klandingham/Blinds_Control/Example_Projects/Servo_Adapter_for_Automated_Blinds/images/df64a273555f48d18f35c3c6244d9a91_preview_featured.jpg

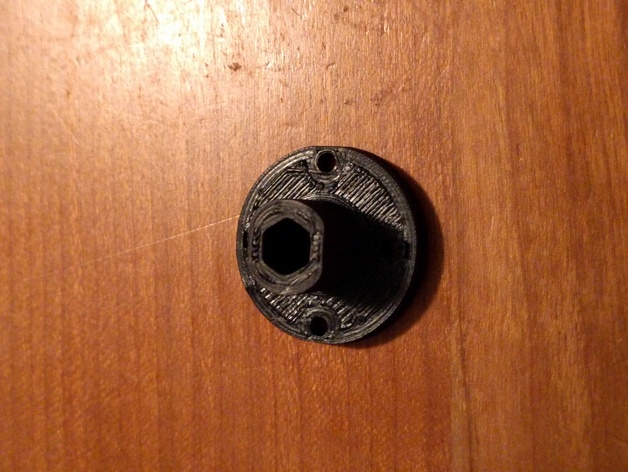
Example_Projects/Servo_Adapter_for_Automated_Blinds/images/df64a273555f48d18f35c3c6244d9a91_preview_featured.jpg
