klandingham/Blinds_Control/Example_Projects/Servo_adapter_for_blinds/images/5d1fb73a9985321ed66258ca8657291f_preview_featured.jpg

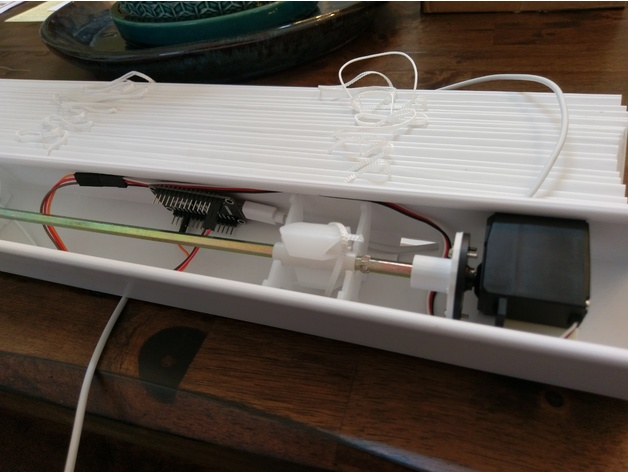
Example_Projects/Servo_adapter_for_blinds/images/5d1fb73a9985321ed66258ca8657291f_preview_featured.jpg
