klandingham/Blinds_Control/Datasheets/VS1838 datasheet_files/1_data/13673994358968836068.jpeg

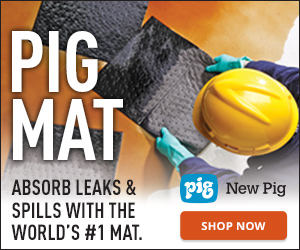
Datasheets/VS1838 datasheet_files/1_data/13673994358968836068.jpeg
