klandingham/Blinds_Control/Diagrams/74HC595_IO_expansion_sample_circuit.jpg

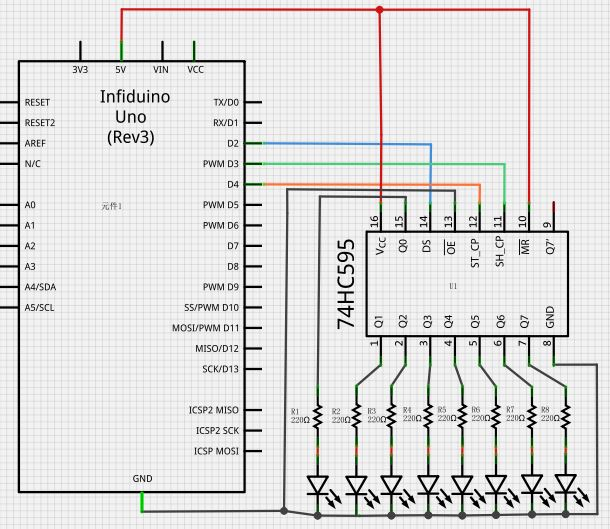
Diagrams/74HC595_IO_expansion_sample_circuit.jpg
