klandingham/Blinds_Control/Diagrams/Board Layout Labeled.jpg

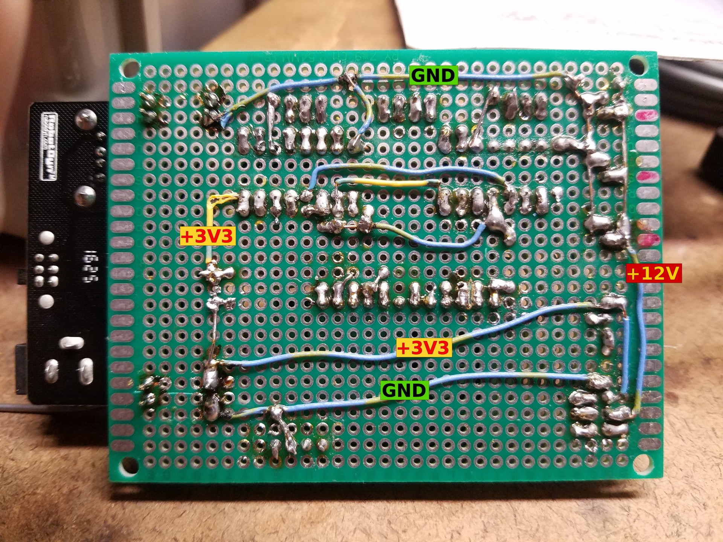
Diagrams/Board Layout Labeled.jpg
