klandingham/Blinds_Control/Diagrams/Breadboard/v2/Breadboard-2.jpg

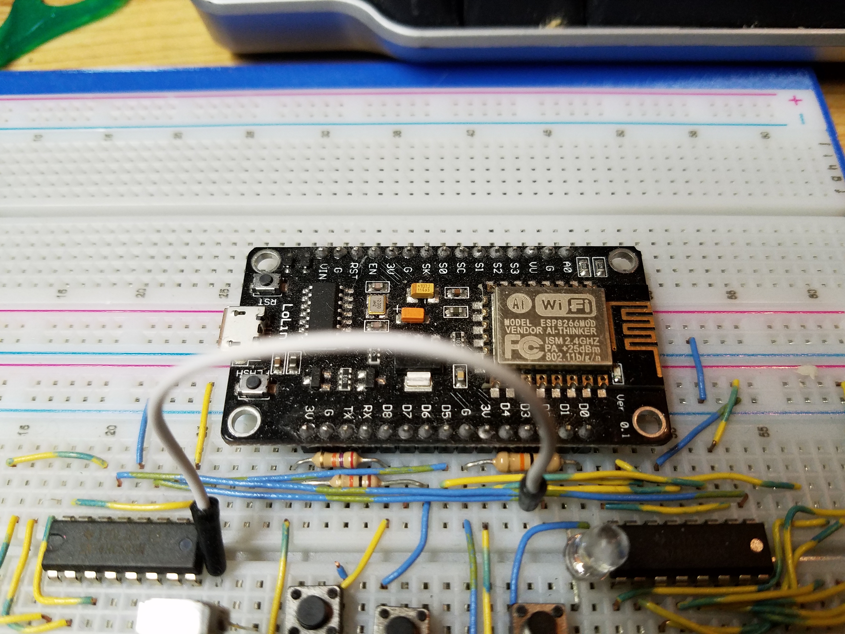
Diagrams/Breadboard/v2/Breadboard-2.jpg
