klandingham/Blinds_Control/Diagrams/Breadboard/v2/Breadboard-3.jpg

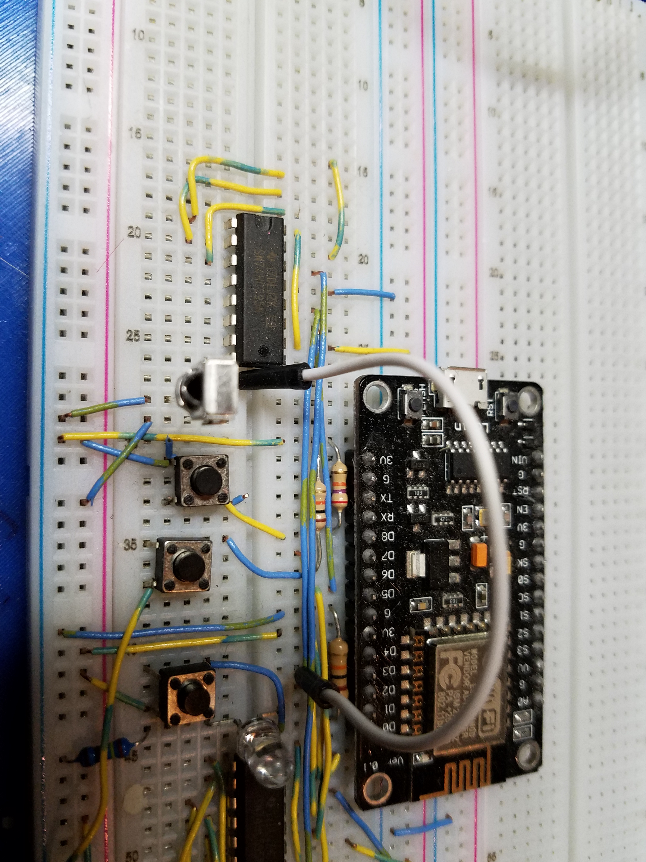
Diagrams/Breadboard/v2/Breadboard-3.jpg
