klandingham/Blinds_Control/Diagrams/J7_pins.jpg

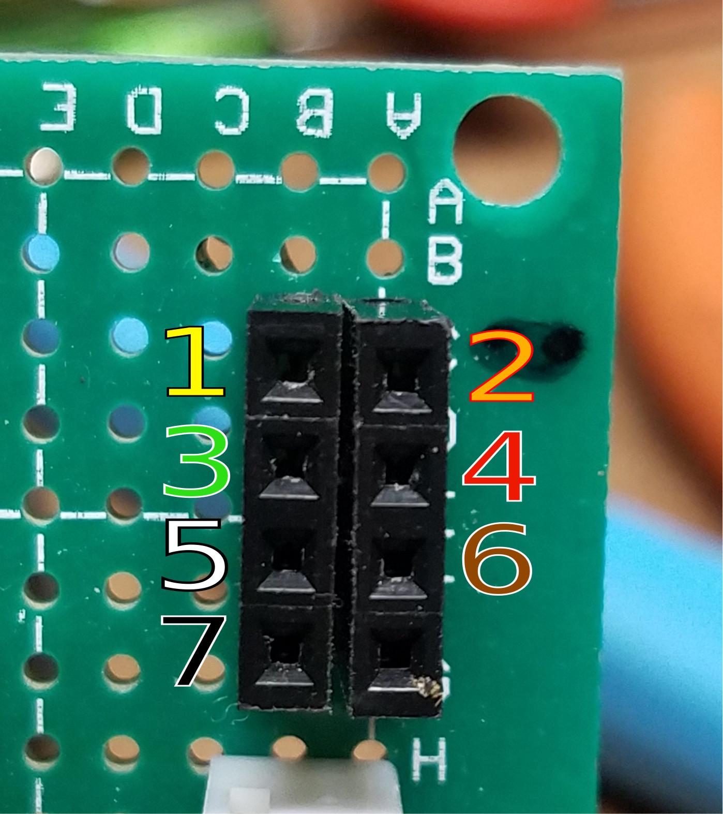
Diagrams/J7_pins.jpg
