klandingham/Blinds_Control/Diagrams/pushbutton-diagram.jpg

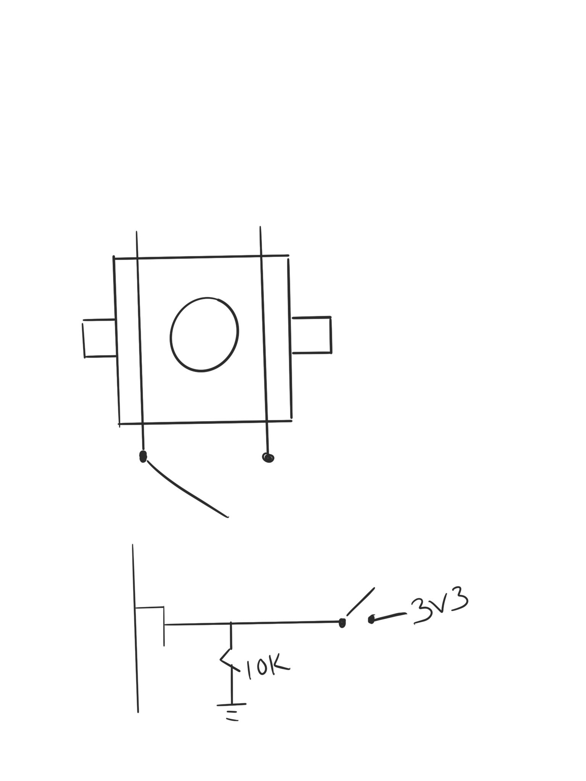
Diagrams/pushbutton-diagram.jpg
