klandingham/Blinds_Control/Example_Projects/Automated_window_blinds/images/0dbd72139b1b72931606092e1da129da_preview_featured.jpg

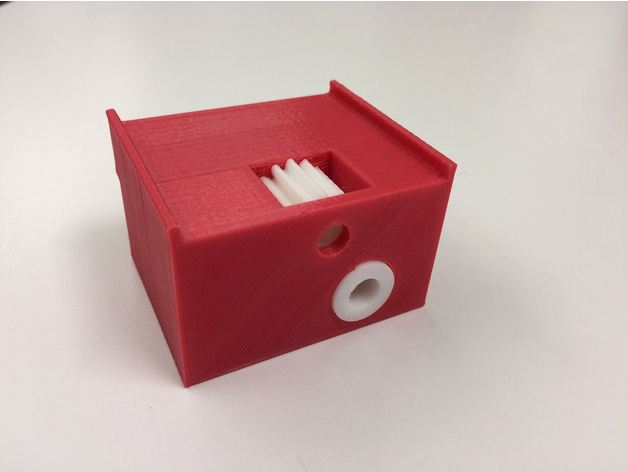
Example_Projects/Automated_window_blinds/images/0dbd72139b1b72931606092e1da129da_preview_featured.jpg
