klandingham/Blinds_Control/Example_Projects/Automated_window_blinds/images/2a1e8ae209445f8ed7df08887682355c_preview_featured.jpg

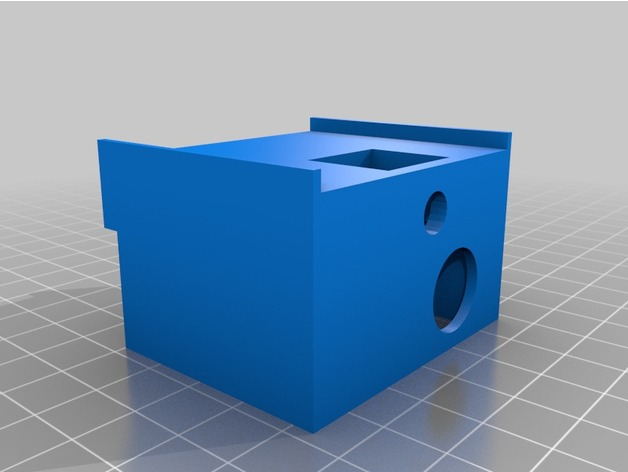
Example_Projects/Automated_window_blinds/images/2a1e8ae209445f8ed7df08887682355c_preview_featured.jpg
