klandingham/Blinds_Control/Example_Projects/Automated_window_blinds/images/3be72de2d3ea145a1b588abaab555e87_preview_featured.jpg

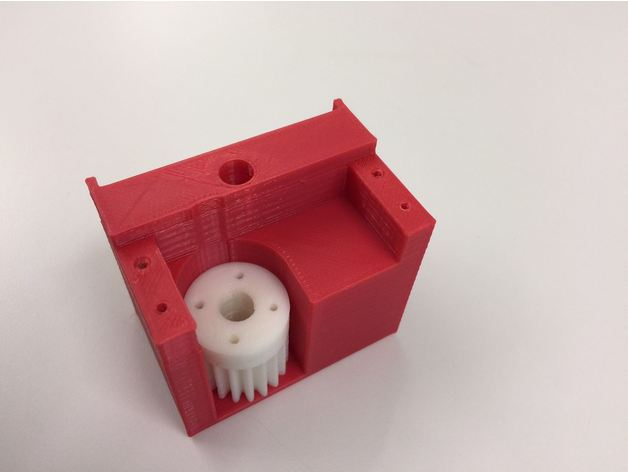
Example_Projects/Automated_window_blinds/images/3be72de2d3ea145a1b588abaab555e87_preview_featured.jpg
