klandingham/Blinds_Control/Example_Projects/Automated_window_blinds/images/7c7b84c2f0f5334c513f18091b792038_preview_featured.jpg

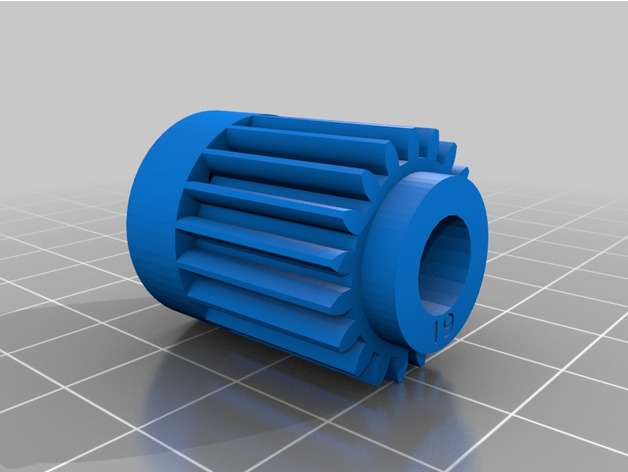
Example_Projects/Automated_window_blinds/images/7c7b84c2f0f5334c513f18091b792038_preview_featured.jpg
