klandingham/Blinds_Control/Example_Projects/Automated_window_blinds/images/51a1170ac061b8a56ec46677e9c119d1_preview_featured.jpg

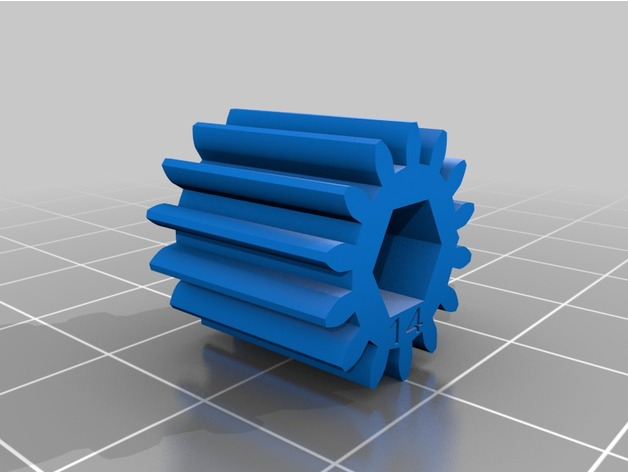
Example_Projects/Automated_window_blinds/images/51a1170ac061b8a56ec46677e9c119d1_preview_featured.jpg
