klandingham/Blinds_Control/Example_Projects/Automated_window_blinds/images/d08ca0e88c3ed342fe436adfcc059d2c_preview_featured.jpg

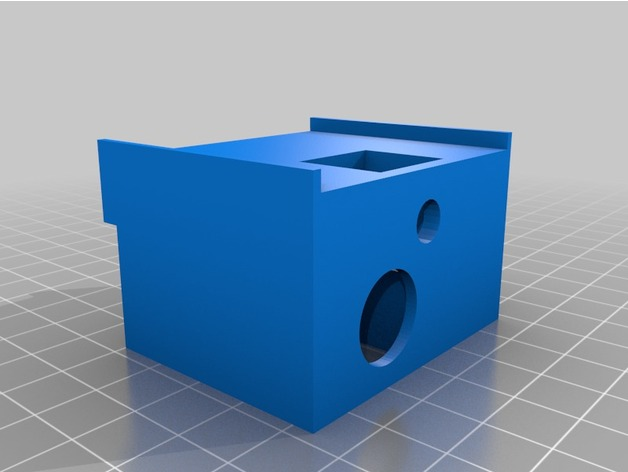
Example_Projects/Automated_window_blinds/images/d08ca0e88c3ed342fe436adfcc059d2c_preview_featured.jpg
