klandingham/Blinds_Control/Example_Projects/Blinds_Stepper_Motor_Controller/images/0ca458882b988e988b201099f90ac491_preview_featured.jpg

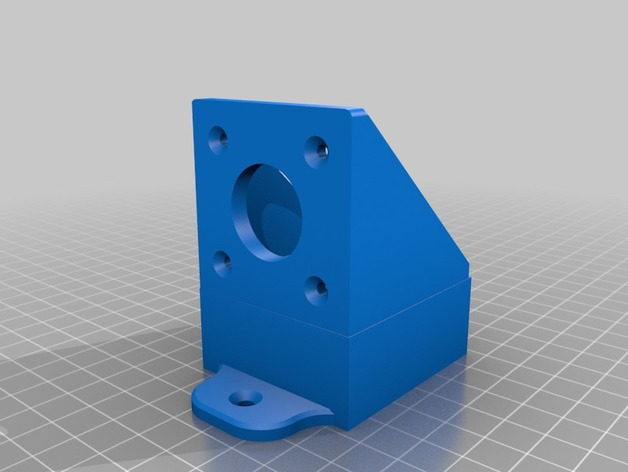
Example_Projects/Blinds_Stepper_Motor_Controller/images/0ca458882b988e988b201099f90ac491_preview_featured.jpg
