klandingham/Blinds_Control/Example_Projects/Blinds_Stepper_Motor_Controller/images/94a17963498ac2957ab965c8fd468688_preview_featured.jpg

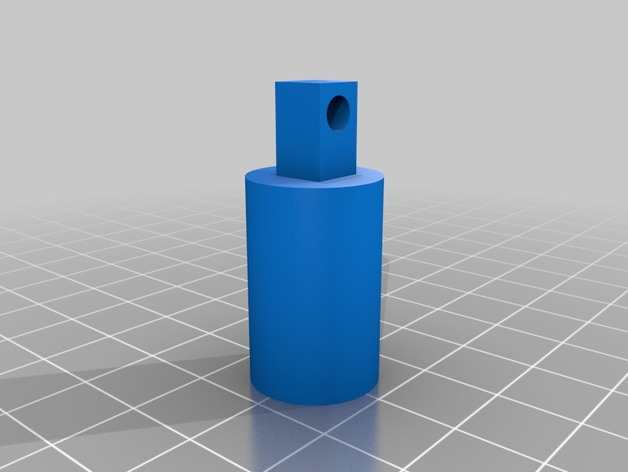
Example_Projects/Blinds_Stepper_Motor_Controller/images/94a17963498ac2957ab965c8fd468688_preview_featured.jpg
