klandingham/Blinds_Control/Example_Projects/Blinds_Stepper_Motor_Controller/images/799bad5a3b514f096e69bbc4a7896cd9_preview_featured.jpg

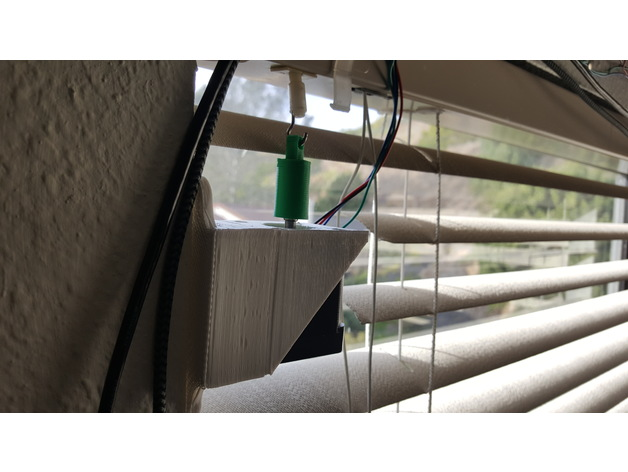
Example_Projects/Blinds_Stepper_Motor_Controller/images/799bad5a3b514f096e69bbc4a7896cd9_preview_featured.jpg
