klandingham/Blinds_Control/Example_Projects/Blinds_Stepper_Motor_Controller/images/d0096ec6c83575373e3a21d129ff8fef_preview_featured.jpg

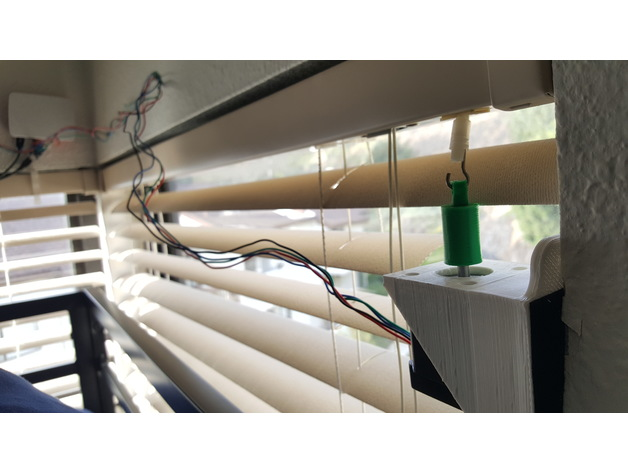
Example_Projects/Blinds_Stepper_Motor_Controller/images/d0096ec6c83575373e3a21d129ff8fef_preview_featured.jpg
