klandingham/Blinds_Control/Example_Projects/Blinds_Stepper_Motor_Controller/images/f3ccdd27d2000e3f9255a7e3e2c48800_preview_featured.jpg

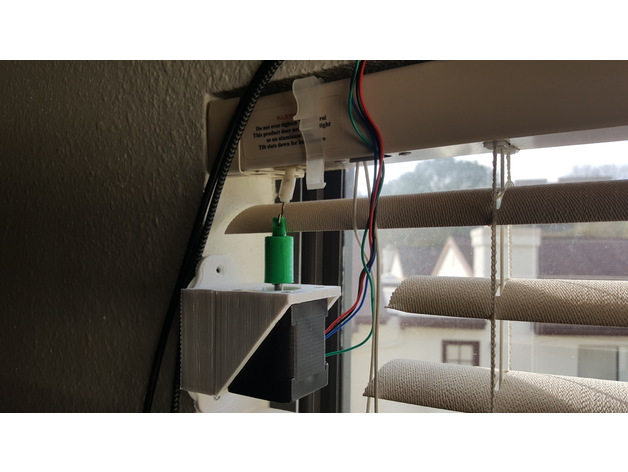
Example_Projects/Blinds_Stepper_Motor_Controller/images/f3ccdd27d2000e3f9255a7e3e2c48800_preview_featured.jpg
