klandingham/Blinds_Control/Example_Projects/Servo_Adapter_for_Automated_Blinds/images/8d56957c13c70d7b545bc574395df51b_preview_featured.jpg

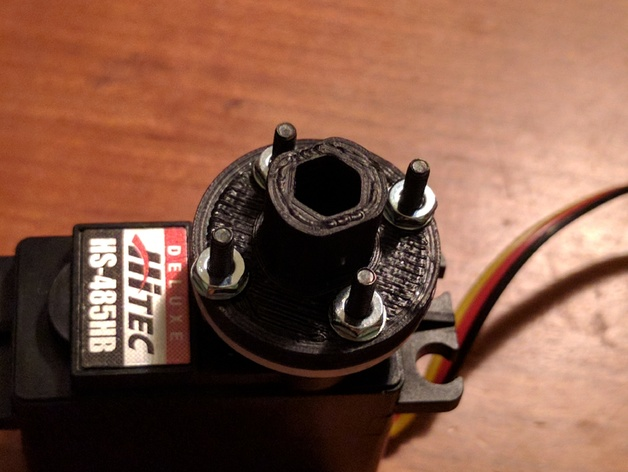
Example_Projects/Servo_Adapter_for_Automated_Blinds/images/8d56957c13c70d7b545bc574395df51b_preview_featured.jpg
