klandingham/Blinds_Control/Example_Projects/Servo_Adapter_for_Automated_Blinds/images/43b85763882b75d2b69c953d2dd04455_preview_featured.jpg

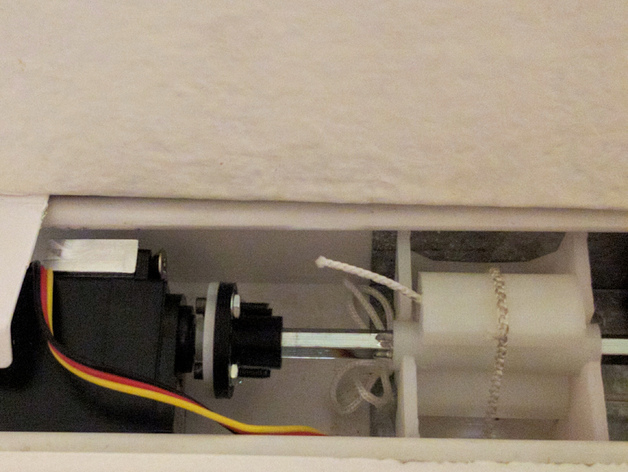
Example_Projects/Servo_Adapter_for_Automated_Blinds/images/43b85763882b75d2b69c953d2dd04455_preview_featured.jpg
