klandingham/Blinds_Control/Example_Projects/Servo_Adapter_for_Automated_Blinds/images/0583f7e29a5a532bcb58fbe3828fd911_preview_featured.jpg

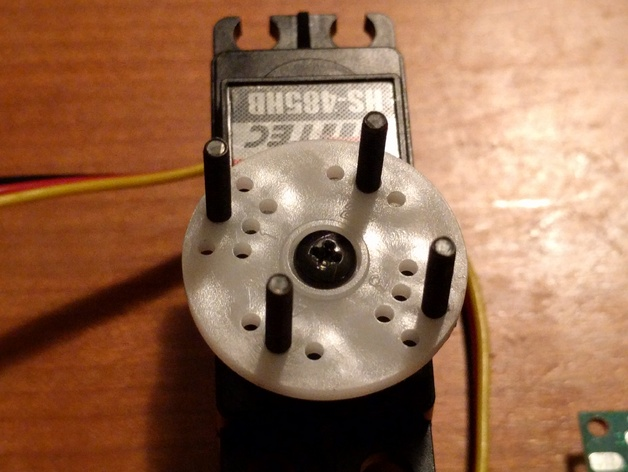
Example_Projects/Servo_Adapter_for_Automated_Blinds/images/0583f7e29a5a532bcb58fbe3828fd911_preview_featured.jpg
