klandingham/Blinds_Control/Example_Projects/Servo_Adapter_for_Automated_Blinds/images/242499b90d92d8a3c1900d62b4687f6d_preview_featured.jpg

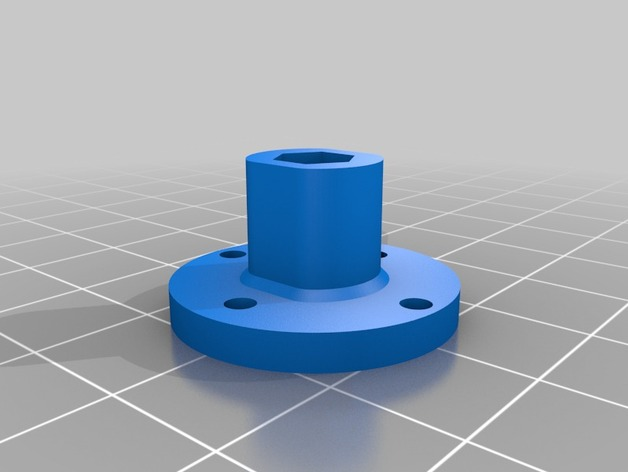
Example_Projects/Servo_Adapter_for_Automated_Blinds/images/242499b90d92d8a3c1900d62b4687f6d_preview_featured.jpg
