klandingham/Blinds_Control/Example_Projects/Servo_adapter_for_blinds/images/8e7e8af2247d28f97953c48f6f39e9a5_preview_featured.jpg

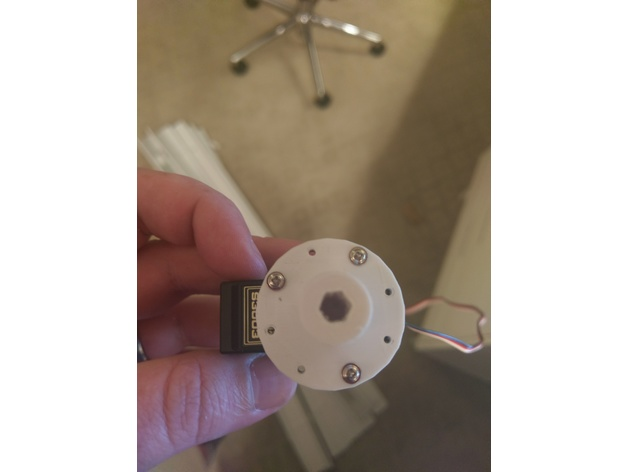
Example_Projects/Servo_adapter_for_blinds/images/8e7e8af2247d28f97953c48f6f39e9a5_preview_featured.jpg
