klandingham/Blinds_Control/Example_Projects/Servo_adapter_for_blinds/images/4008a9b219bc578ee4de48e5d4f73412_preview_featured.jpg

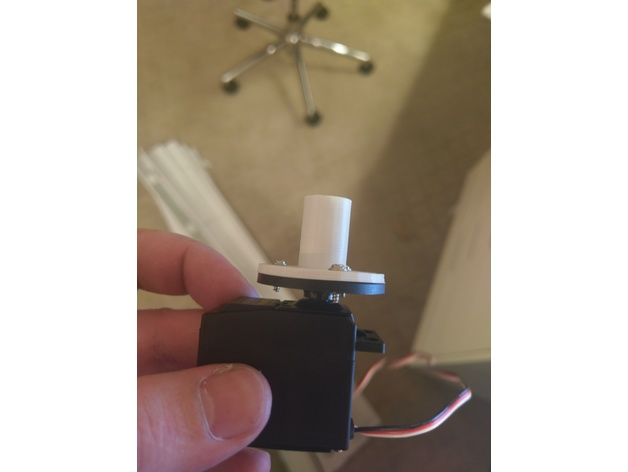
Example_Projects/Servo_adapter_for_blinds/images/4008a9b219bc578ee4de48e5d4f73412_preview_featured.jpg
