klandingham/Blinds_Control/Example_Projects/Servo_adapter_for_blinds/images/8679c8f7650d90e7cc76d3c26cc39134_preview_featured.jpg

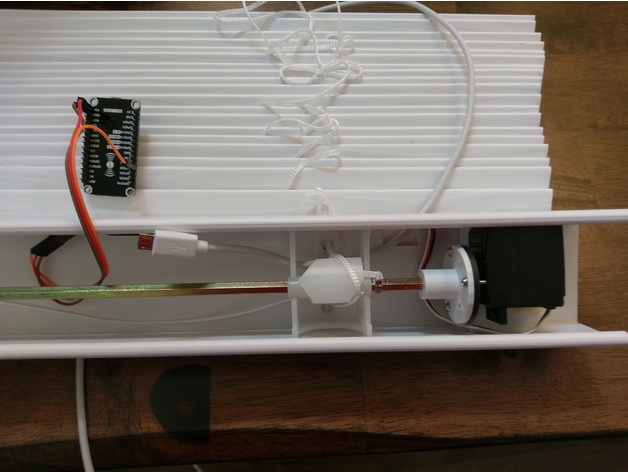
Example_Projects/Servo_adapter_for_blinds/images/8679c8f7650d90e7cc76d3c26cc39134_preview_featured.jpg
