klandingham/Blinds_Control/Example_Projects/Servo_adapter_for_blinds/images/c9348f00d997d8b843449cc2bac39666_preview_featured.jpg

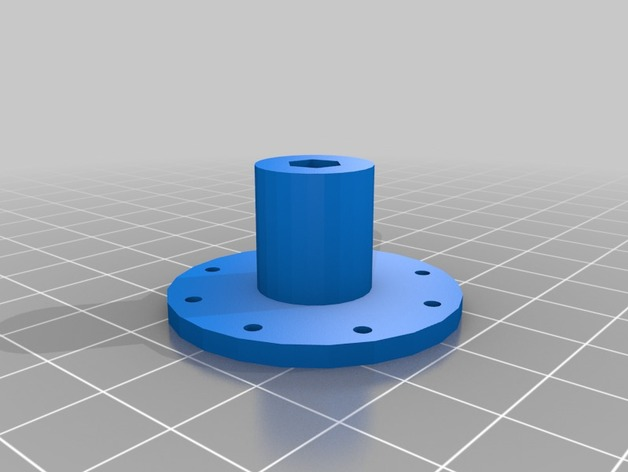
Example_Projects/Servo_adapter_for_blinds/images/c9348f00d997d8b843449cc2bac39666_preview_featured.jpg
