klandingham/Blinds_Control/Example_Projects/Servo_adapter_for_blinds/images/f5c94f27fc36e1c8725ffeb552db501e_preview_featured.jpg

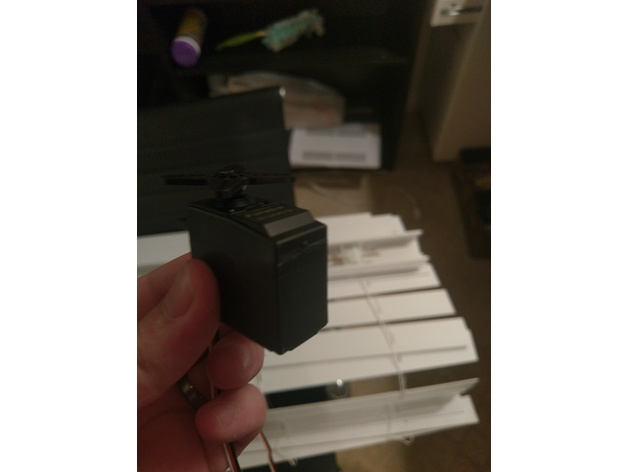
Example_Projects/Servo_adapter_for_blinds/images/f5c94f27fc36e1c8725ffeb552db501e_preview_featured.jpg
