klandingham/Blinds_Control/Example_Projects/WiFi_Window-Blinds_Roller/images/7b7e7c0269467608b5808af1a2d691ca_preview_featured.jpg

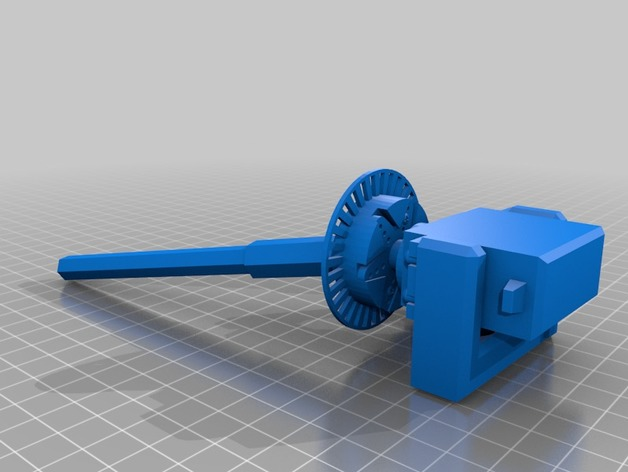
Example_Projects/WiFi_Window-Blinds_Roller/images/7b7e7c0269467608b5808af1a2d691ca_preview_featured.jpg
