klandingham/Blinds_Control/Example_Projects/WiFi_Window-Blinds_Roller/images/9c8a4cd324916dcc4e85334bb4fedf4f_preview_featured.JPG

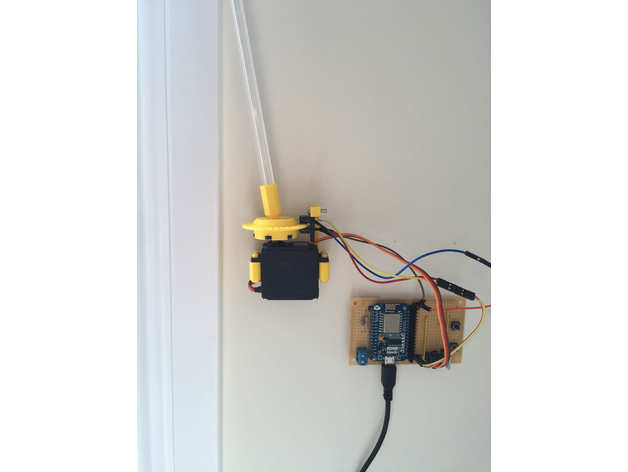
Example_Projects/WiFi_Window-Blinds_Roller/images/9c8a4cd324916dcc4e85334bb4fedf4f_preview_featured.JPG
