klandingham/Blinds_Control/Example_Projects/WiFi_Window-Blinds_Roller/images/47e4459eb694de2b554587ecafb3ef61_preview_featured.jpg

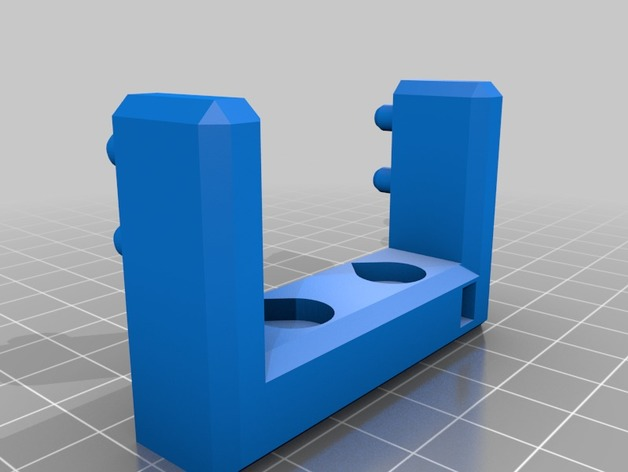
Example_Projects/WiFi_Window-Blinds_Roller/images/47e4459eb694de2b554587ecafb3ef61_preview_featured.jpg
