klandingham/Blinds_Control/Example_Projects/WiFi_Window-Blinds_Roller/images/64f70ef4e7e904f5829ffbd56e4282fa_preview_featured.jpg

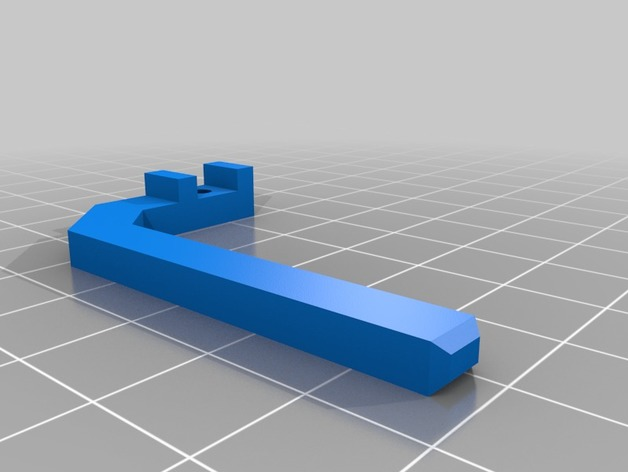
Example_Projects/WiFi_Window-Blinds_Roller/images/64f70ef4e7e904f5829ffbd56e4282fa_preview_featured.jpg
