klandingham/Blinds_Control/Example_Projects/WiFi_Window-Blinds_Roller/images/93ce8574e1e4e3efcc80637c74880ca0_preview_featured.jpg

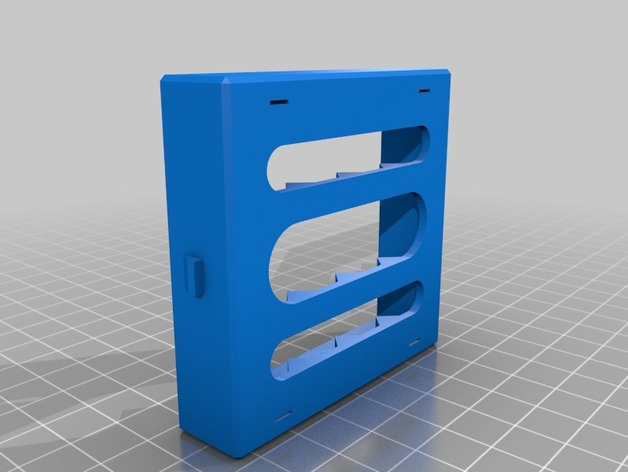
Example_Projects/WiFi_Window-Blinds_Roller/images/93ce8574e1e4e3efcc80637c74880ca0_preview_featured.jpg
