klandingham/Blinds_Control/Example_Projects/WiFi_Window-Blinds_Roller/images/aa77651dd114ddc3b98a7daae5970775_preview_featured.jpg

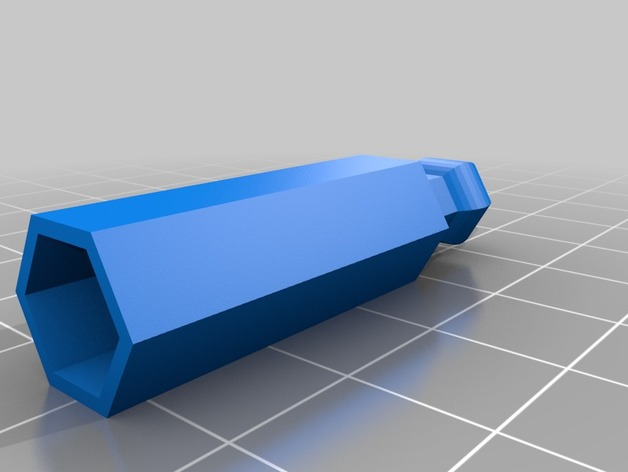
Example_Projects/WiFi_Window-Blinds_Roller/images/aa77651dd114ddc3b98a7daae5970775_preview_featured.jpg
