klandingham/Blinds_Control/Example_Projects/Blinds_Stepper_Motor_Controller/files/motor-container.stl

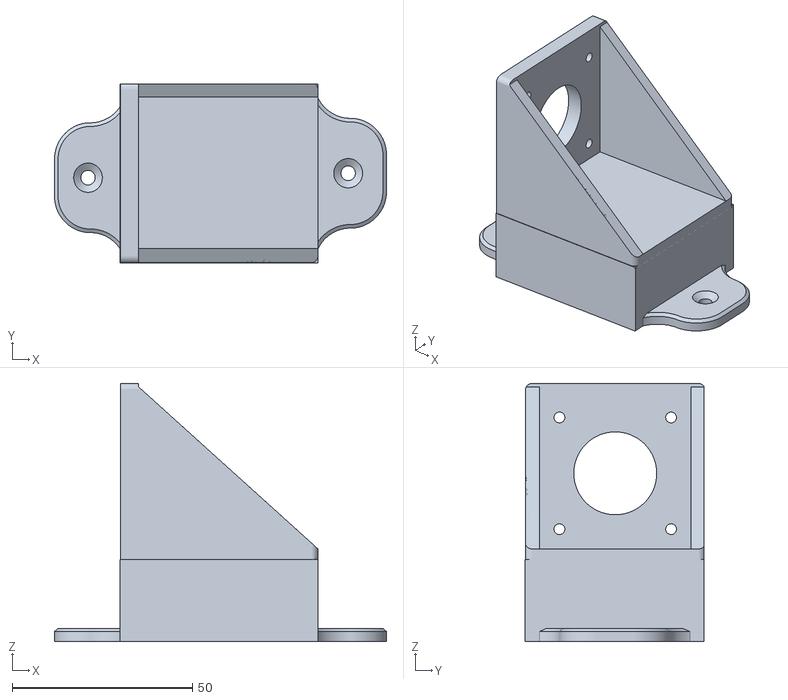
[picture p52: CAD file, 2019-06-21]
Example_Projects/Blinds_Stepper_Motor_Controller/files/motor-container.stl
92.2 x 49.8 x 71.8
