klandingham/Blinds_Control/Example_Projects/BlindsRodAdapter.STL

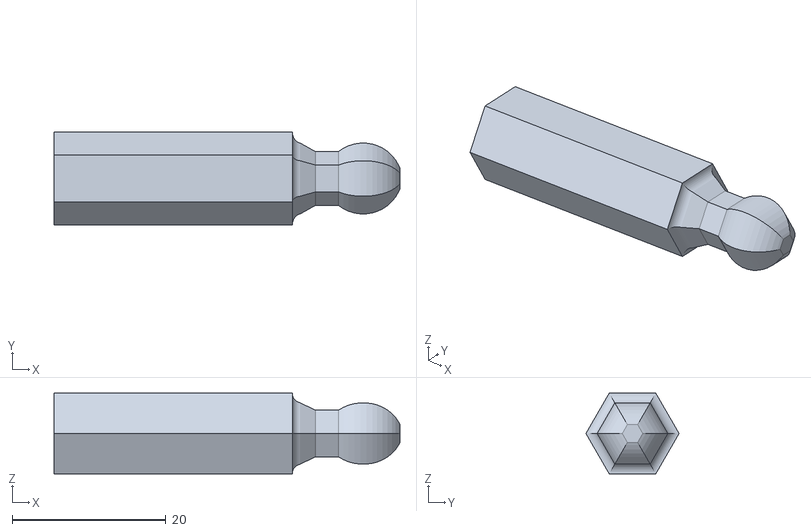
[picture p53: CAD file, 2019-06-21]
Example_Projects/BlindsRodAdapter.STL
45.0 x 12.1 x 10.5
