klandingham/Blinds_Control/stl/Original Design/slip-clutch-plate-v1.stl

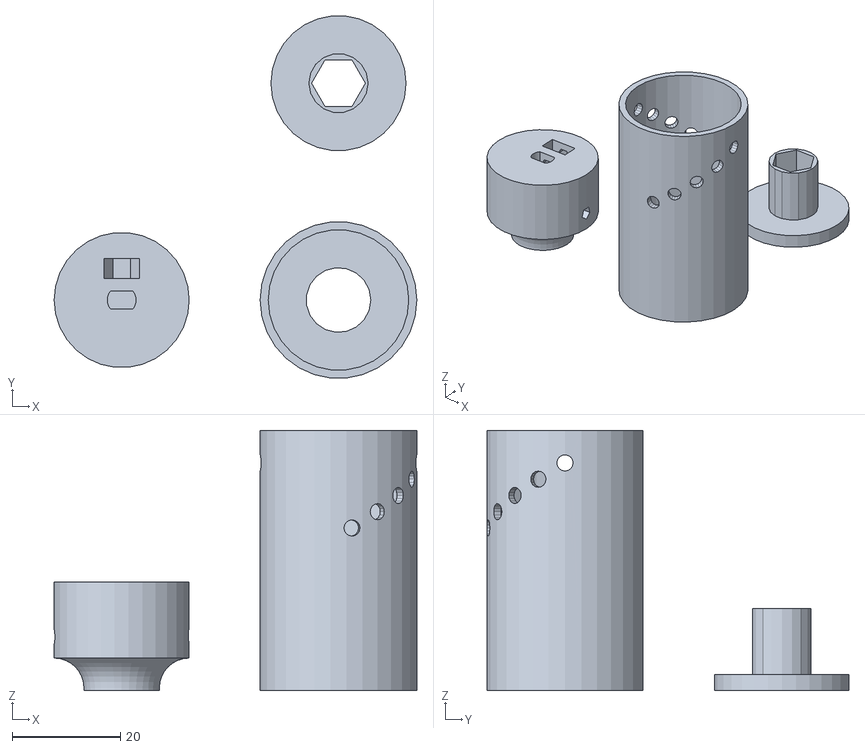
[picture p54: CAD file, 2019-06-21]
stl/Original Design/slip-clutch-plate-v1.stl
66.9 x 66.8 x 48.0
