klandingham/Blinds_Control/stl/Rod Sleeve Mod - 7.9.stl

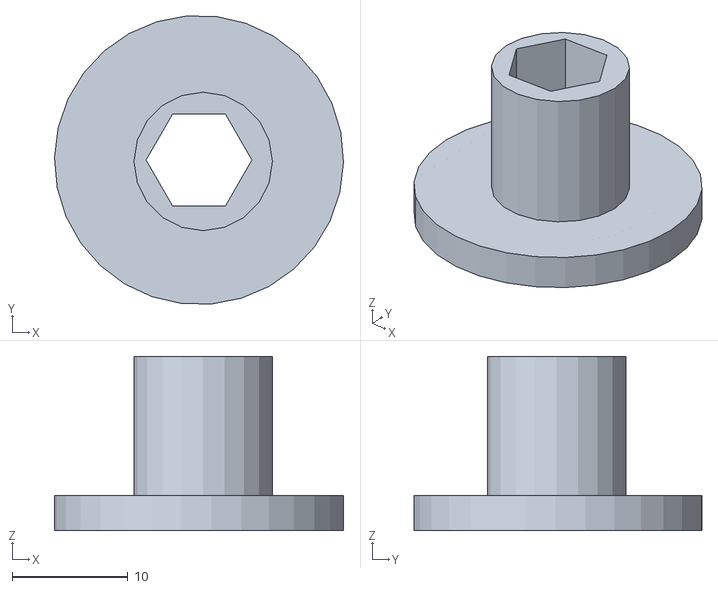
[picture p55: CAD file, 2019-06-21]
stl/Rod Sleeve Mod - 7.9.stl
24.9 x 24.8 x 15.0
