klandingham/Blinds_Control/Example_Projects/Automated_window_blinds/files/Offset_Geared_Servo_Blinds.stl.stl

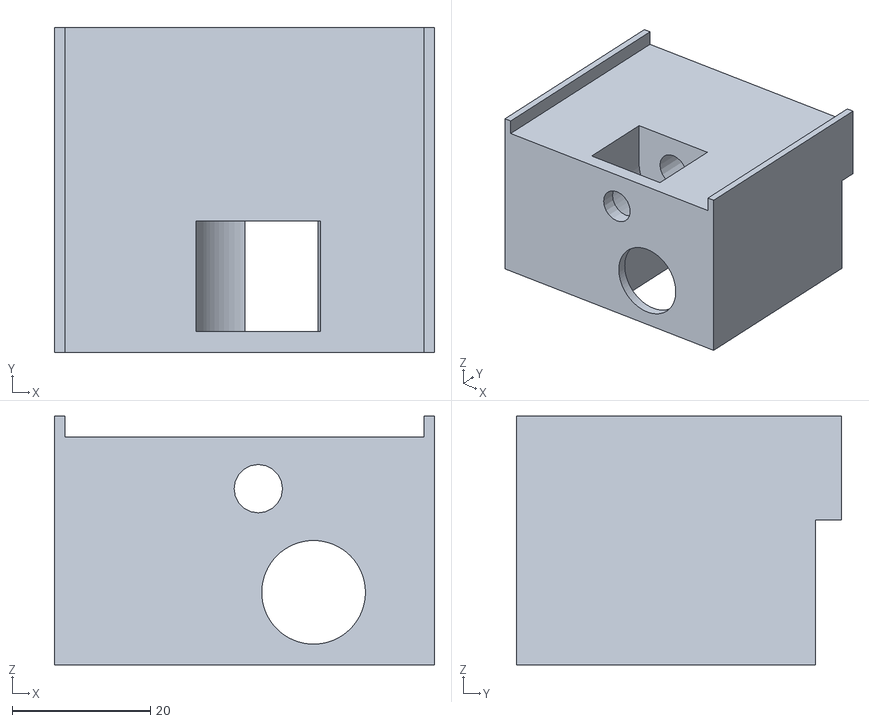
[picture p56: CAD file, 2019-06-21]
Example_Projects/Automated_window_blinds/files/Offset_Geared_Servo_Blinds.stl.stl
55.0 x 47.0 x 36.0
