klandingham/Blinds_Control/Example_Projects/WiFi_Window-Blinds_Roller/files/ServoMount.STL

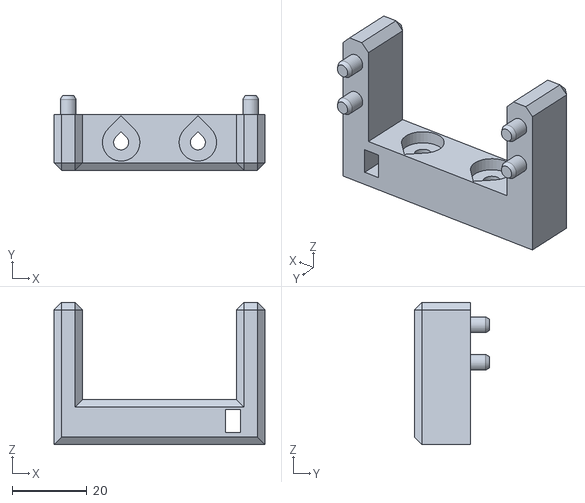
[picture p57: CAD file, 2019-06-21]
Example_Projects/WiFi_Window-Blinds_Roller/files/ServoMount.STL
56.3 x 20.0 x 38.0
