klandingham/Blinds_Control/stl/box_cover/button_board_size_test_1.stl

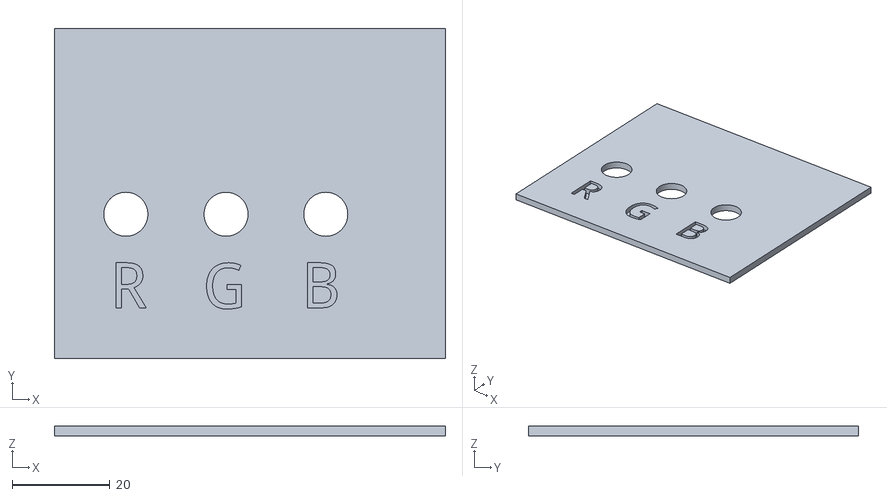
[picture p58: CAD file, 2019-07-14]
stl/box_cover/button_board_size_test_1.stl
80.0 x 67.5 x 2.00
