klandingham/Blinds_Control/stl/Rod Sleeve Mod.stl

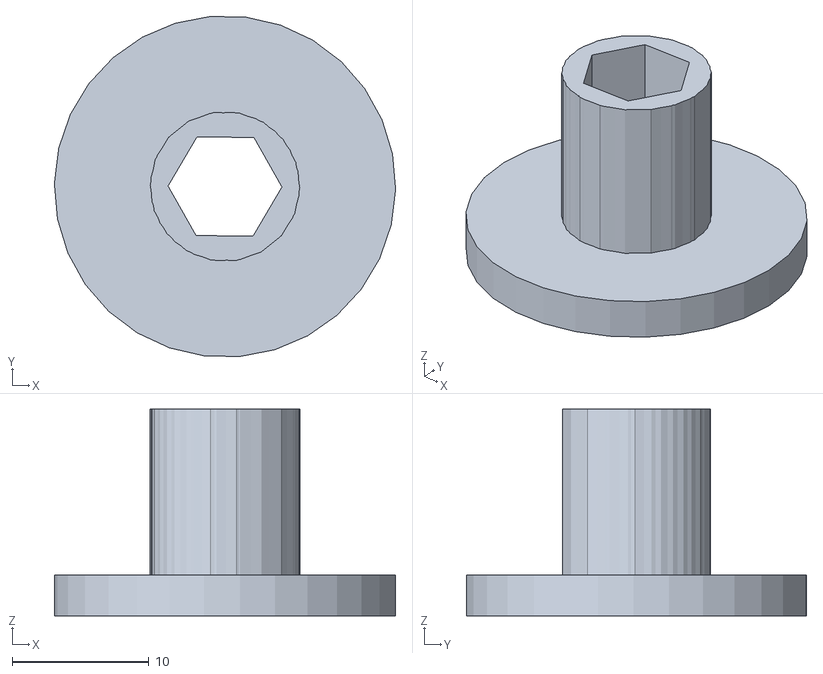
[picture p59: CAD file, 2019-06-21]
stl/Rod Sleeve Mod.stl
24.9 x 24.8 x 15.1
