klandingham/Blinds_Control/Example_Projects/Blinds_Automation_-_using_LinkIt_ONE/servo_horn_v2.stl

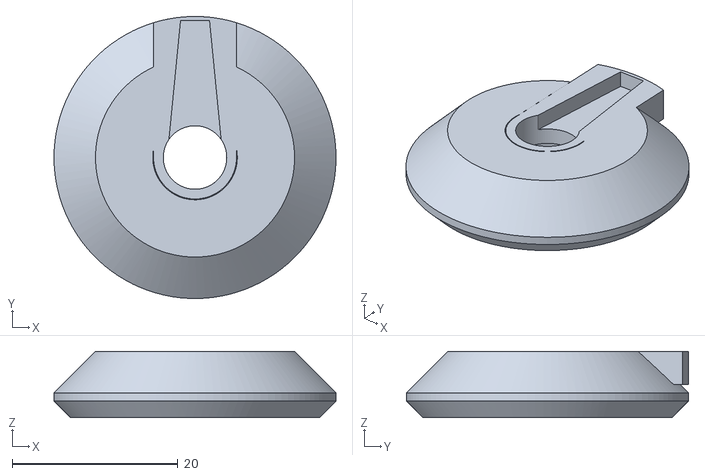
[picture p60: CAD file, 2019-06-21]
Example_Projects/Blinds_Automation_-_using_LinkIt_ONE/servo_horn_v2.stl
34.0 x 34.0 x 8.00
