klandingham/Blinds_Control/Example_Projects/WiFi_Window-Blinds_Roller/files/BatteryBox-4.STL

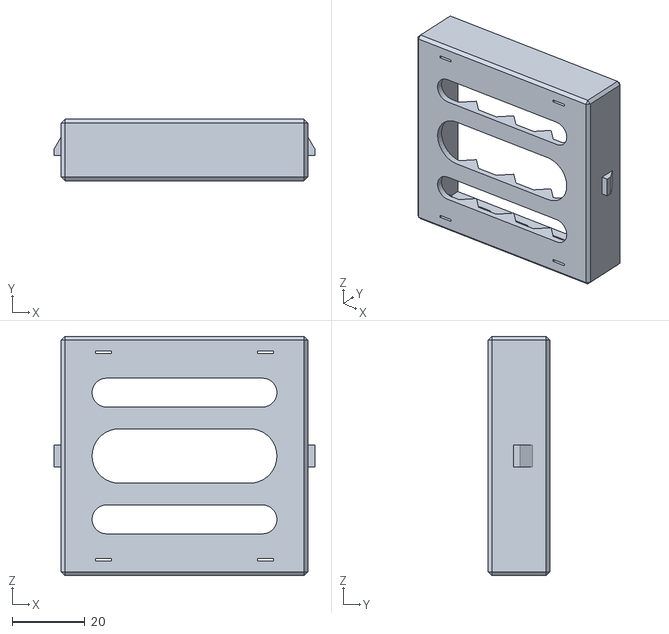
[picture p61: CAD file, 2019-06-21]
Example_Projects/WiFi_Window-Blinds_Roller/files/BatteryBox-4.STL
72.0 x 17.0 x 66.0
