klandingham/Blinds_Control/stl/box_cover/button_spacing_test.stl

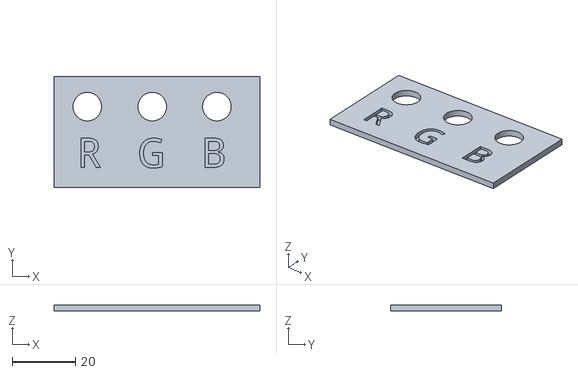
[picture p62: CAD file, 2019-07-09]
stl/box_cover/button_spacing_test.stl
65.0 x 35.0 x 2.00
