klandingham/Blinds_Control/stl/Rod Sleeve Size Test - 7.9.stl

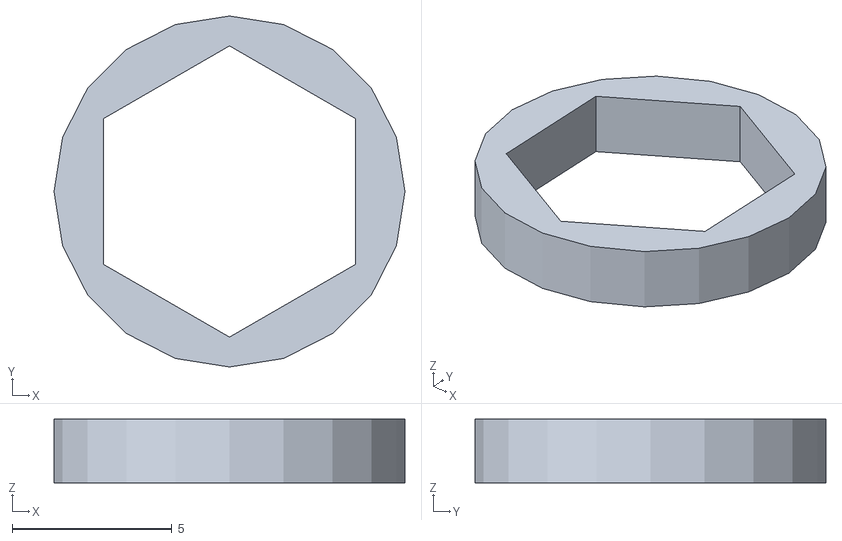
[picture p63: CAD file, 2019-06-21]
stl/Rod Sleeve Size Test - 7.9.stl
11.0 x 11.0 x 2.00
