klandingham/Blinds_Control/Example_Projects/BlindZer-master/3D STL Files/Assemly_PREVIEW.STL

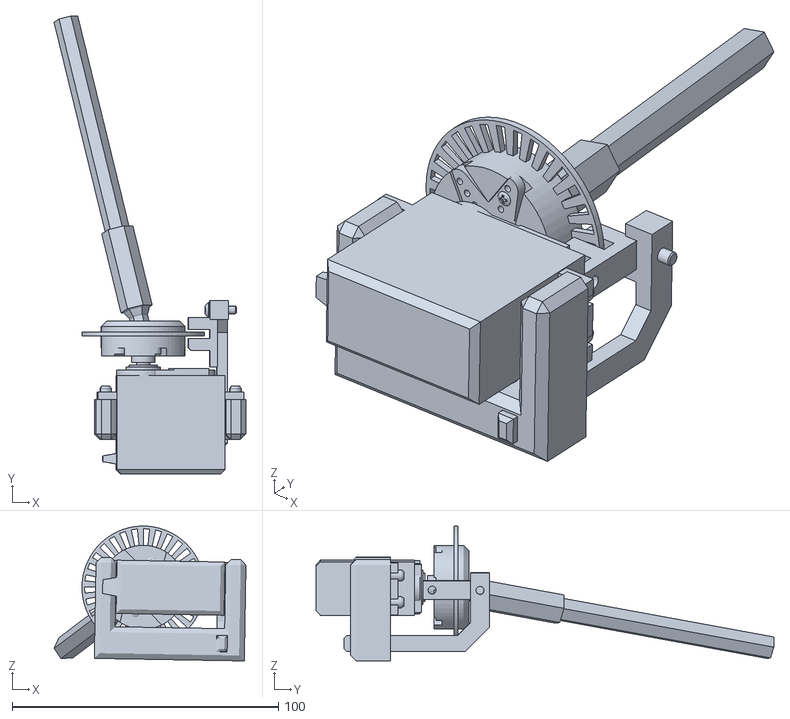
[picture p64: CAD file, 2019-06-21]
Example_Projects/BlindZer-master/3D STL Files/Assemly_PREVIEW.STL
72.1 x 171.9 x 50.6
