klandingham/Blinds_Control/stl/box_cover/button_hole_diam_test.stl

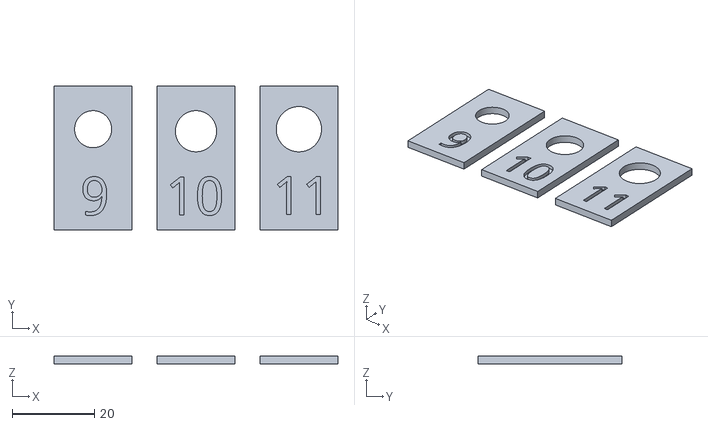
[picture p65: CAD file, 2019-07-07]
stl/box_cover/button_hole_diam_test.stl
69.0 x 35.0 x 2.00
