klandingham/Blinds_Control/stl/box_cover/box.stl

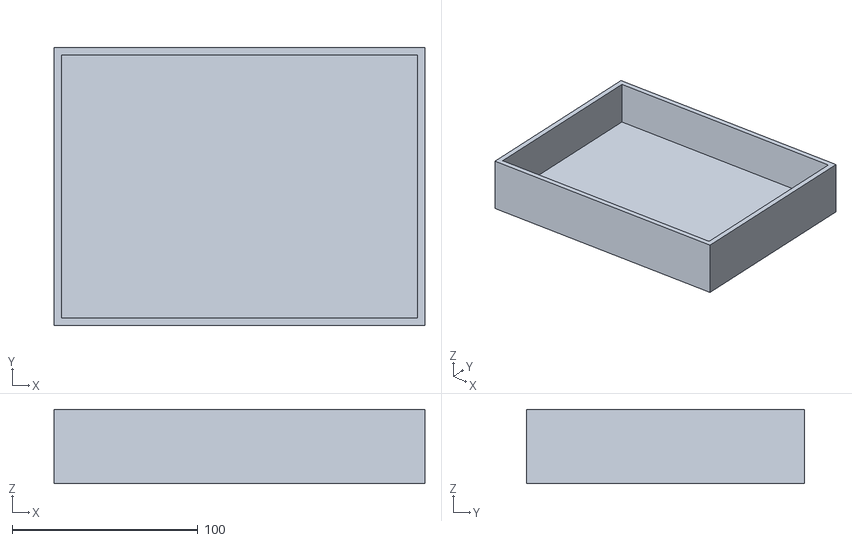
[picture p66: CAD file, 2019-07-07]
stl/box_cover/box.stl
200.0 x 150.0 x 40.0
