klandingham/Blinds_Control/stl/L Strut (thick).stl

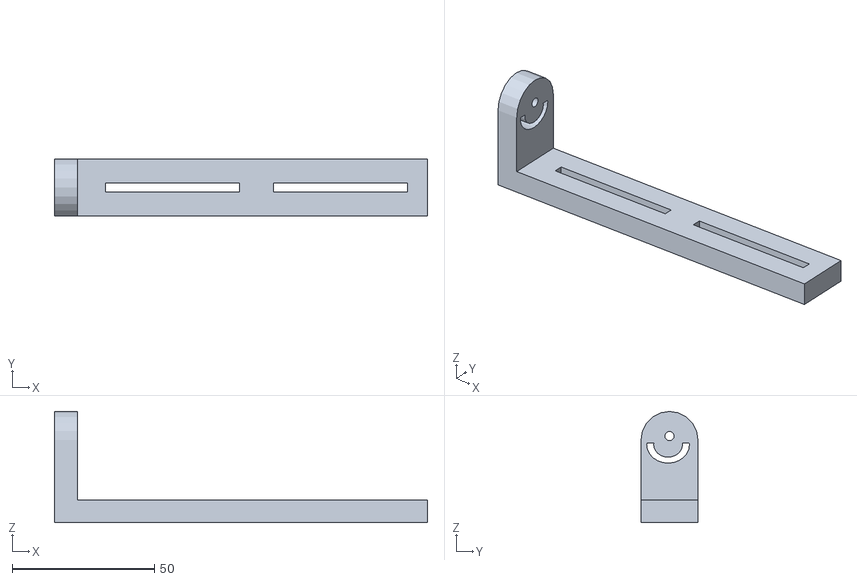
[picture p67: CAD file, 2019-06-21]
stl/L Strut (thick).stl
130.9 x 20.0 x 39.0
