klandingham/Blinds_Control/stl/Window Trim Mount (contour test smoothed).stl

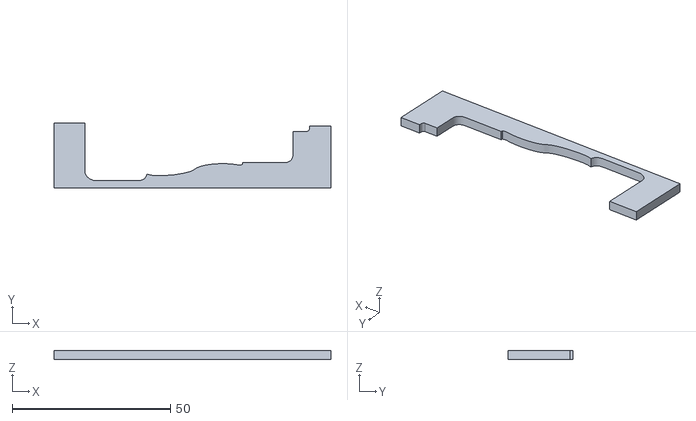
[picture p68: CAD file, 2019-06-21]
stl/Window Trim Mount (contour test smoothed).stl
87.5 x 20.6 x 2.80
