klandingham/Blinds_Control/stl/L Strut.stl

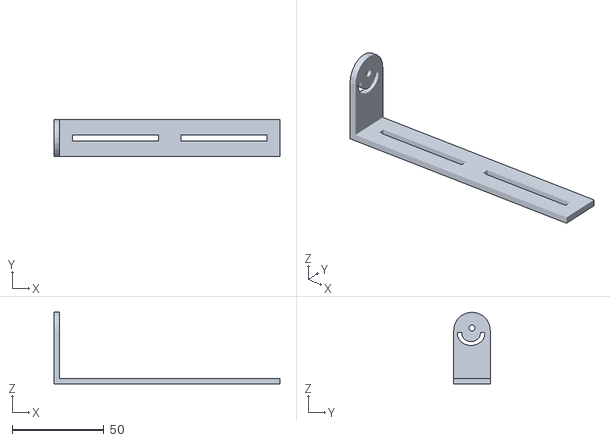
[picture p69: CAD file, 2019-06-21]
stl/L Strut.stl
123.0 x 20.0 x 39.0
