klandingham/Blinds_Control/stl/Window Trim Mount (contour test).stl

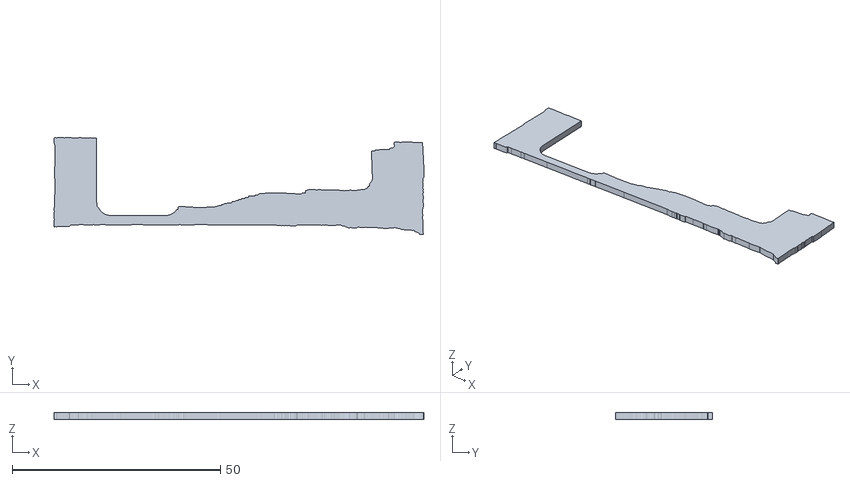
[picture p70: CAD file, 2019-06-21]
stl/Window Trim Mount (contour test).stl
88.9 x 23.4 x 1.57
