klandingham/Blinds_Control/stl/Window Trim Mount Base v3.stl

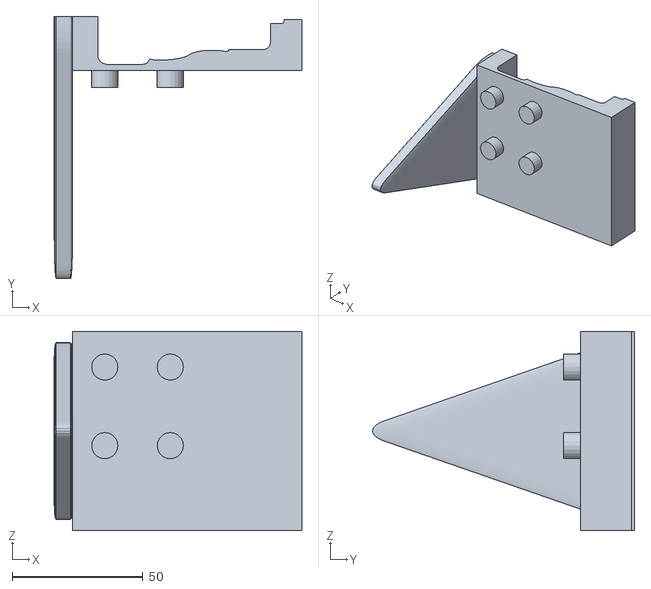
[picture p71: CAD file, 2019-06-21]
stl/Window Trim Mount Base v3.stl
94.5 x 100.0 x 76.0
