klandingham/Blinds_Control/stl/Blind Clutch Motor Hub Mod 1.stl

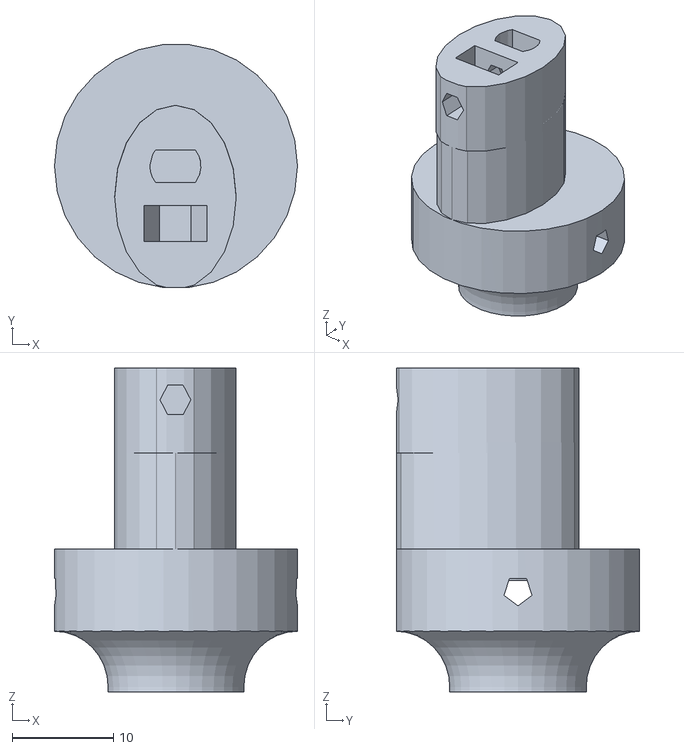
[picture p72: CAD file, 2019-06-21]
stl/Blind Clutch Motor Hub Mod 1.stl
24.0 x 24.0 x 32.0
