klandingham/Blinds_Control/stl/Blinds Clutch Spring Cup (enlarged hole).stl

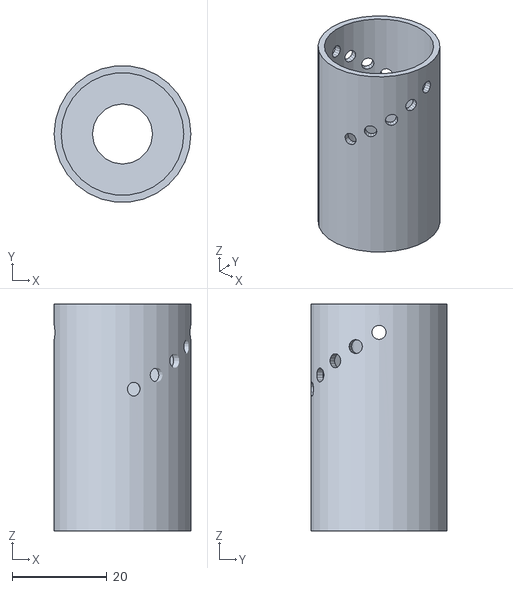
[picture p73: CAD file, 2019-06-21]
stl/Blinds Clutch Spring Cup (enlarged hole).stl
28.9 x 28.8 x 48.0
