klandingham/Blinds_Control/stl/Window Trim Mount Side Plate.stl

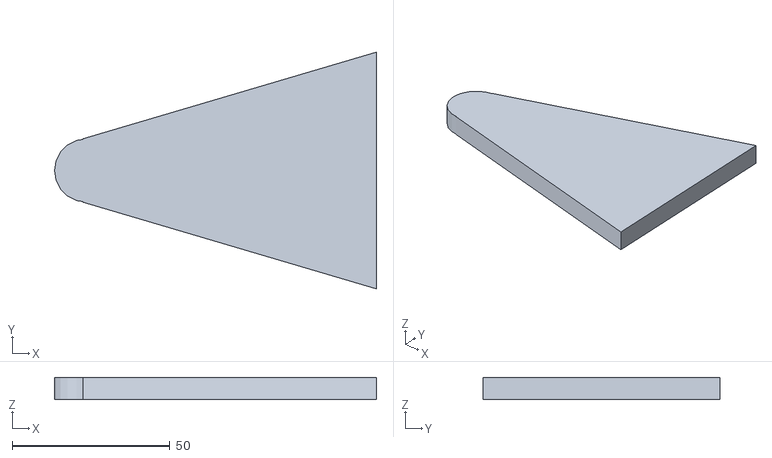
[picture p74: CAD file, 2019-06-21]
stl/Window Trim Mount Side Plate.stl
102.0 x 75.0 x 7.00
