klandingham/Blinds_Control/Diagrams/KiCAD/V3-working/V3.kicad_pcb

## KiCad design kicad/Eprommer.sch

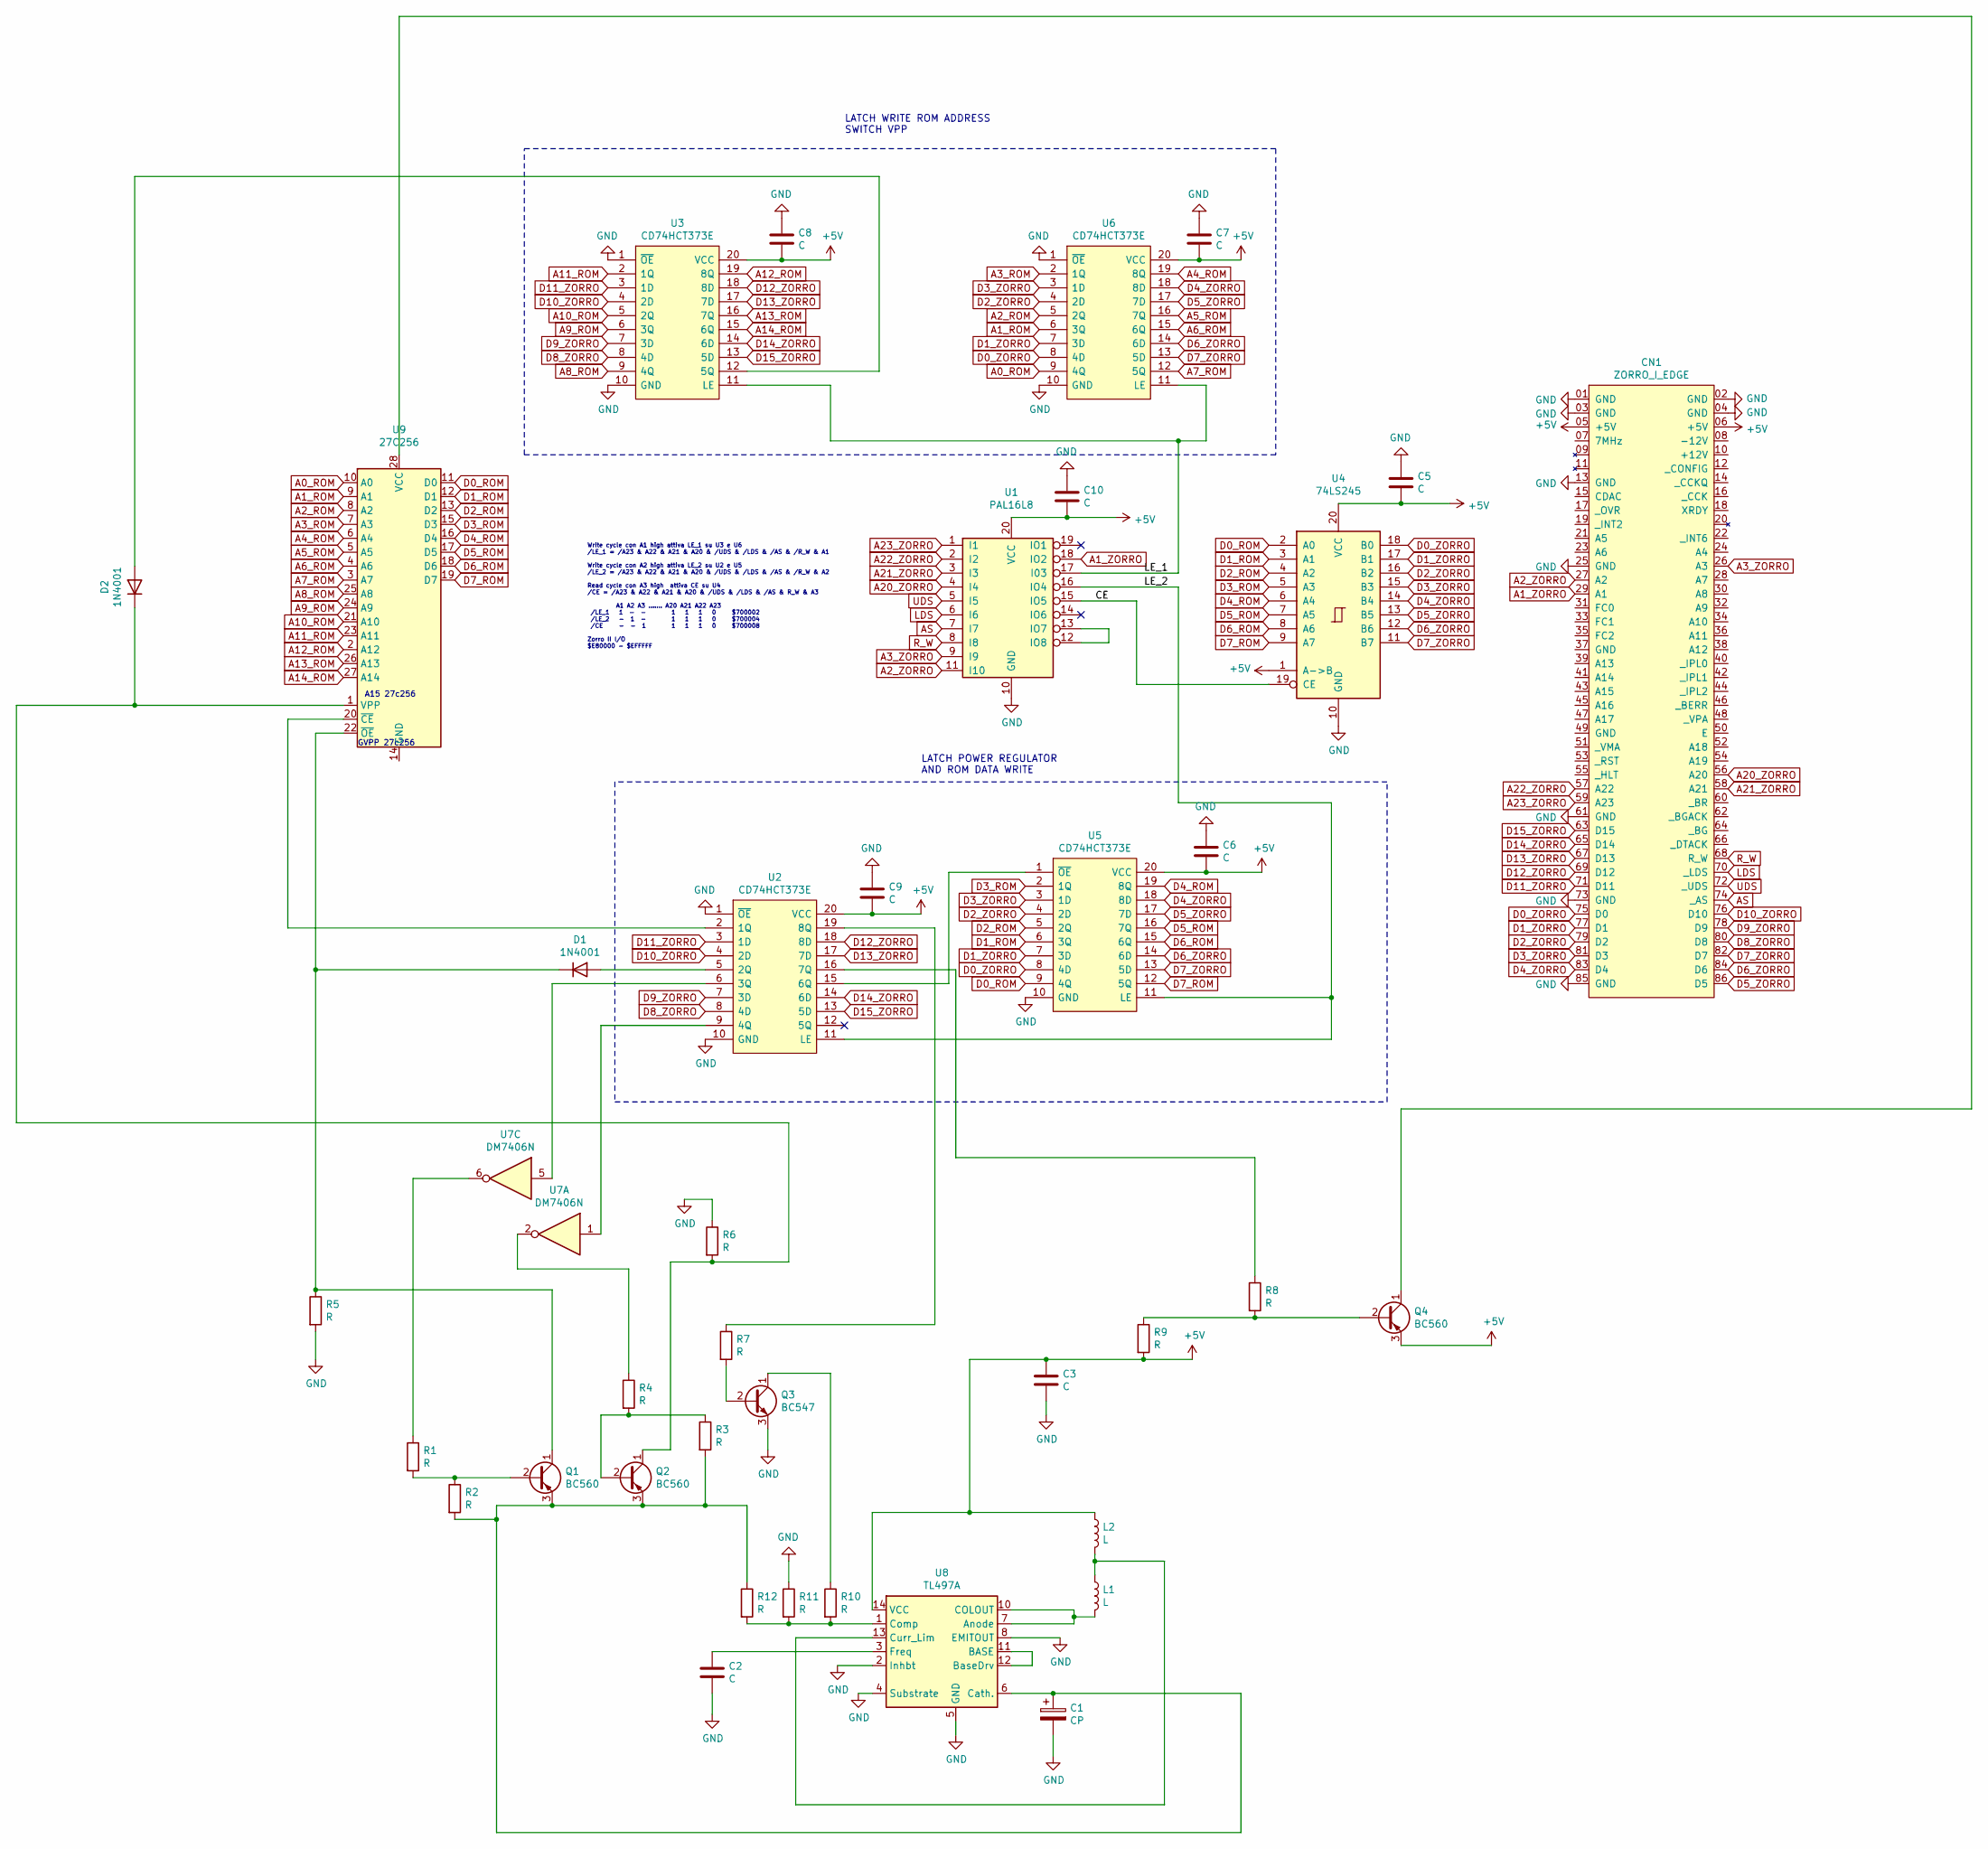
[picture p75: schematic Eprommer.sch]

Parts:
C1: CP
C2, C3, C5, C6, C7, C8, C9, C10: C
CN1: ZORRO_I_EDGE
D1, D2: 1N4001; D_DO-41_SOD81_P10.16mm_Horizontal
L1, L2: L
Q1, Q2, Q4: BC560; TO-92_Inline
Q3: BC547; TO-92_Inline
R1, R2, R3, R4, R5, R6, R7, R8, R9, R10, R11, R12: R
U1: PAL16L8
U2, U3, U5, U6: CD74HCT373E; DIP794W53P254L2540H508Q20N; Mouser Part Number 595-CD74HCT373E
U4: 74LS245
U7: DM7406N
U8: TL497A
U9: 27C256; DIP-28_W15.24mm

Connections:
+5V: C3.1, C5.2, C6.2, C7.2, C8.2, C9.2, C10.2, CN1.05 (+5V), CN1.06 (+5V), L2.1, Q4.3 (E), R9.2, U1.20 (VCC), U2.20 (VCC), U3.20 (VCC), U4.1 (A->B), U4.20 (VCC), U5.20 (VCC), U6.20 (VCC), U8.14 (VCC)
A0_ROM: U6.9 (4Q), U9.10 (A0)
A1_ROM: U6.6 (3Q), U9.9 (A1)
A1_ZORRO: CN1.29 (A1), U1.18 (IO2)
A2_ROM: U6.5 (2Q), U9.8 (A2)
A2_ZORRO: CN1.27 (A2), U1.11 (I10)
A3_ROM: U6.2 (1Q), U9.7 (A3)
A3_ZORRO: CN1.26 (A3), U1.9 (I9)
A4_ROM: U6.19 (8Q), U9.6 (A4)
A5_ROM: U6.16 (7Q), U9.5 (A5)
A6_ROM: U6.15 (6Q), U9.4 (A6)
A7_ROM: U6.12 (5Q), U9.3 (A7)
A8_ROM: U3.9 (4Q), U9.25 (A8)
A9_ROM: U3.6 (3Q), U9.24 (A9)
A10_ROM: U3.5 (2Q), U9.21 (A10)
A11_ROM: U3.2 (1Q), U9.23 (A11)
A12_ROM: U3.19 (8Q), U9.2 (A12)
A13_ROM: U3.16 (7Q), U9.26 (A13)
A14_ROM: U3.15 (6Q), U9.27 (A14)
A20_ZORRO: CN1.56 (A20), U1.4 (I4)
A21_ZORRO: CN1.58 (A21), U1.3 (I3)
A22_ZORRO: CN1.57 (A22), U1.2 (I2)
A23_ZORRO: CN1.59 (A23), U1.1 (I1)
AS: CN1.74 (_AS), U1.7 (I7)
CE: U1.15 (IO5), U4.19 (CE)
D0_ROM: U4.2 (A0), U5.9 (4Q), U9.11 (D0)
D0_ZORRO: CN1.75 (D0), U4.18 (B0), U5.8 (4D), U6.8 (4D)
D1_ROM: U4.3 (A1), U5.6 (3Q), U9.12 (D1)
D1_ZORRO: CN1.77 (D1), U4.17 (B1), U5.7 (3D), U6.7 (3D)
D2_ROM: U4.4 (A2), U5.5 (2Q), U9.13 (D2)
D2_ZORRO: CN1.79 (D2), U4.16 (B2), U5.4 (2D), U6.4 (2D)
D3_ROM: U4.5 (A3), U5.2 (1Q), U9.15 (D3)
D3_ZORRO: CN1.81 (D3), U4.15 (B3), U5.3 (1D), U6.3 (1D)
D4_ROM: U4.6 (A4), U5.19 (8Q), U9.16 (D4)
D4_ZORRO: CN1.83 (D4), U4.14 (B4), U5.18 (8D), U6.18 (8D)
D5_ROM: U4.7 (A5), U5.16 (7Q), U9.17 (D5)
D5_ZORRO: CN1.86 (D5), U4.13 (B5), U5.17 (7D), U6.17 (7D)
D6_ROM: U4.8 (A6), U5.15 (6Q), U9.18 (D6)
D6_ZORRO: CN1.84 (D6), U4.12 (B6), U5.14 (6D), U6.14 (6D)
D7_ROM: U4.9 (A7), U5.12 (5Q), U9.19 (D7)
D7_ZORRO: CN1.82 (D7), U4.11 (B7), U5.13 (5D), U6.13 (5D)
D8_ZORRO: CN1.80 (D8), U2.8 (4D), U3.8 (4D)
D9_ZORRO: CN1.78 (D9), U2.7 (3D), U3.7 (3D)
D10_ZORRO: CN1.76 (D10), U2.4 (2D), U3.4 (2D)
D11_ZORRO: CN1.71 (D11), U2.3 (1D), U3.3 (1D)
D12_ZORRO: CN1.69 (D12), U2.18 (8D), U3.18 (8D)
D13_ZORRO: CN1.67 (D13), U2.17 (7D), U3.17 (7D)
D14_ZORRO: CN1.65 (D14), U2.14 (6D), U3.14 (6D)
D15_ZORRO: CN1.63 (D15), U2.13 (5D), U3.13 (5D)
GND: C1.2, C2.2, C3.2, C5.1, C6.1, C7.1, C8.1, C9.1, C10.1, CN1.01 (GND), CN1.02 (GND), CN1.03 (GND), CN1.04 (GND), CN1.13 (GND), CN1.25 (GND), CN1.61 (GND), CN1.73 (GND), CN1.85 (GND), Q3.3 (E), R5.2, R6.1, R11.1, U1.10 (GND), U2.1 (~OE), U2.10 (GND), U3.1 (~OE), U3.10 (GND), U4.10 (GND), U5.10 (GND), U6.1 (~OE), U6.10 (GND), U8.2 (Inhbt), U8.4 (Substrate), U8.5 (GND), U8.8 (EMITOUT)
LDS: CN1.70 (_LDS), U1.6 (I6)
LE_1: U1.17 (I03), U3.11 (LE), U6.11 (LE)
LE_2: U1.16 (IO4), U2.11 (LE), U5.11 (LE)
unnamed: C1.1, Q1.3 (E), Q2.3 (E), R2.2, R3.2, R12.1, U8.6 (Cath.)
unnamed: C2.1, U8.3 (Freq)
unnamed: D1.1 (K), Q1.1 (C), R5.1, U9.22 (~OE)
unnamed: D1.2 (A), U2.5 (2Q)
unnamed: D2.1 (K), Q2.1 (C), R6.2, U9.1 (VPP)
unnamed: D2.2 (A), U3.12 (5Q)
unnamed: L1.1, L2.2, U8.13 (Curr_Lim)
unnamed: L1.2, U8.7 (Anode), U8.10 (COLOUT)
unnamed: Q1.2 (B), R1.2, R2.1
unnamed: Q2.2 (B), R3.1, R4.2
unnamed: Q3.1 (C), R10.1
unnamed: Q3.2 (B), R7.2
unnamed: Q4.1 (C), U9.28 (VCC)
unnamed: Q4.2 (B), R8.2, R9.1
unnamed: R1.1, U7.6
unnamed: R4.1, U7.2
unnamed: R7.1, U2.19 (8Q)
unnamed: R8.1, U2.16 (7Q)
unnamed: R10.2, R11.2, R12.2, U8.1 (Comp)
unnamed: U1.12 (IO8), U1.13 (IO7)
unnamed: U2.2 (1Q), U9.20 (~CE)
unnamed: U2.6 (3Q), U7.5
unnamed: U2.9 (4Q), U7.1
unnamed: U2.15 (6Q), U5.1 (~OE)
unnamed: U8.11 (BASE), U8.12 (BaseDrv)
R_W: CN1.68 (R_W), U1.8 (I8)
UDS: CN1.72 (_UDS), U1.5 (I5)

Notes on the sheet:
Write cycle con A1 high attiva LE_1 su U3 e U6 /LE_1 = /A23 & A22 & A21 & A20 & /UDS & /LDS & /AS & /R_W & A1 Write cycle con A2 high attiva LE_2 su U2 e U5 /LE_2 = /A23 & A22 & A21 & A20 & /UDS & /LDS & /AS & /R_W & A2 Read cycle con A3 high attiva CE su U4 /CE = /A23 & A22 & A21 & A20 & /UDS & /L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
LATCH WRITE ROM ADDRESS SWITCH VPP
LATCH POWER REGULATOR AND ROM DATA WRITE
A15 27c256
GVPP 27c256
