klandingham/Blinds_Control/src/src/CodeSelect.h

/**
 * Common header file to select main code. Use for switching
 * code for particular boards, running test code, etc.
 */

// ApplicationCode for specific boards

//#define NODE_MCU
//#define WAVGAT

// Testing code

//#define BLINK_TEST
//#define IR_TEST
//#define SERIAL_TEST
//#define NODEMCU_IR_TEST
#define SIGNALS_TEST
