klandingham/Blinds_Control/src/src/BlinkTest.cpp

/*
  Blink

  Turns an LED on for one second, then off for one second, repeatedly.

  Most Arduinos have an on-board LED you can control. On the UNO, MEGA and ZERO
  it is attached to digital pin 13, on MKR1000 on pin 6. LED_BUILTIN is set to
  the correct LED pin independent of which board is used.
  If you want to know what pin the on-board LED is connected to on your Arduino
  model, check the Technical Specs of your board at:
  https://www.arduino.cc/en/Main/Products

  modified 8 May 2015
  by Scott Fitzgerald
  modified 2 Sep 2016
  by Arturo Guadalupi
  modified 8 Sep 2016
  by Colby Newman

  This example code is in the public domain.

  http://www.arduino.cc/en/Tutorial/Blink
*/
#include "CodeSelect.h"
#ifdef BLINK_TEST

#include <Arduino.h>

//const uint8_t LED_PIN = LED_BUILTIN;
const uint8_t LED_PIN = 2;
const uint16_t DELAY = 500;

// the setup function runs once when you press reset or power the board
void setup() {
  // initialize digital pin LED_BUILTIN as an output.
  pinMode(LED_PIN, OUTPUT);
  pinMode(LED_BUILTIN, OUTPUT);
}

// the loop function runs over and over again forever
void loop() {
  digitalWrite(LED_PIN, HIGH);   // turn LED OFF
  digitalWrite(LED_BUILTIN, HIGH);   // turn LED OFF
  delay(DELAY);                       // wait for a second
  digitalWrite(LED_PIN, LOW);    // turn the LED off by making the voltage LOW
  digitalWrite(LED_BUILTIN, LOW);   // turn LED OFF
  delay(DELAY);                       // wait for a second
}
#endif
//#define LED D0            // Led in NodeMCU at pin GPIO16 (D0).
//void setup() {
//pinMode(LED, OUTPUT);    // LED pin as output.
//}
//void loop() {
//digitalWrite(LED, HIGH);// turn the LED off.(Note that LOW is the voltage level but actually
//                        //the LED is on; this is because it is acive low on the ESP8266.
//delay(1000);            // wait for 1 second.
//digitalWrite(LED, LOW); // turn the LED on.
//delay(1000); // wait for 1 second.
//}
