klandingham/Blinds_Control/Diagrams/Breadboard/v2/Breadboard-1.jpg

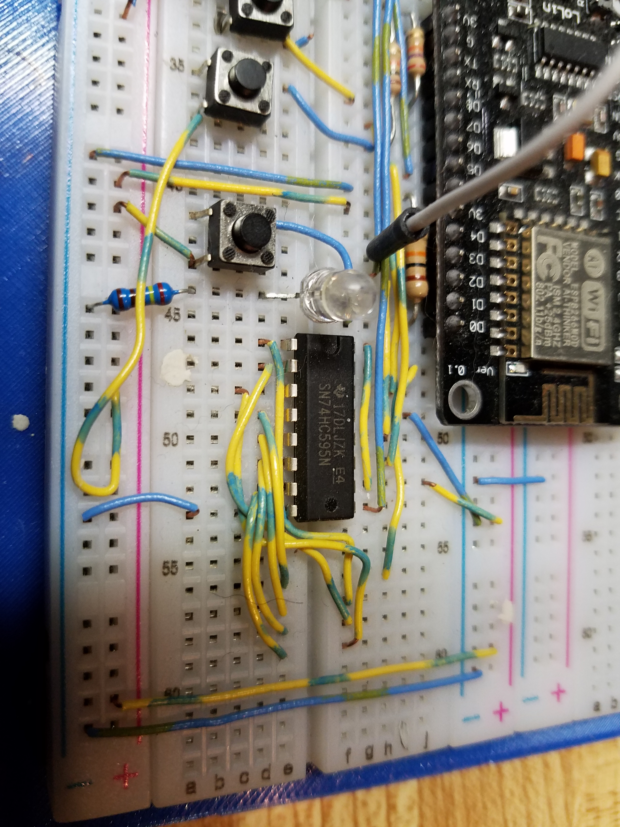
Diagrams/Breadboard/v2/Breadboard-1.jpg
